Freenove/Freenove_Media_Kit_for_ESP32-S3/3D_Models/FNK0102A/3D_Shell_ESP32-S3/CB8201_Bottom.bmp

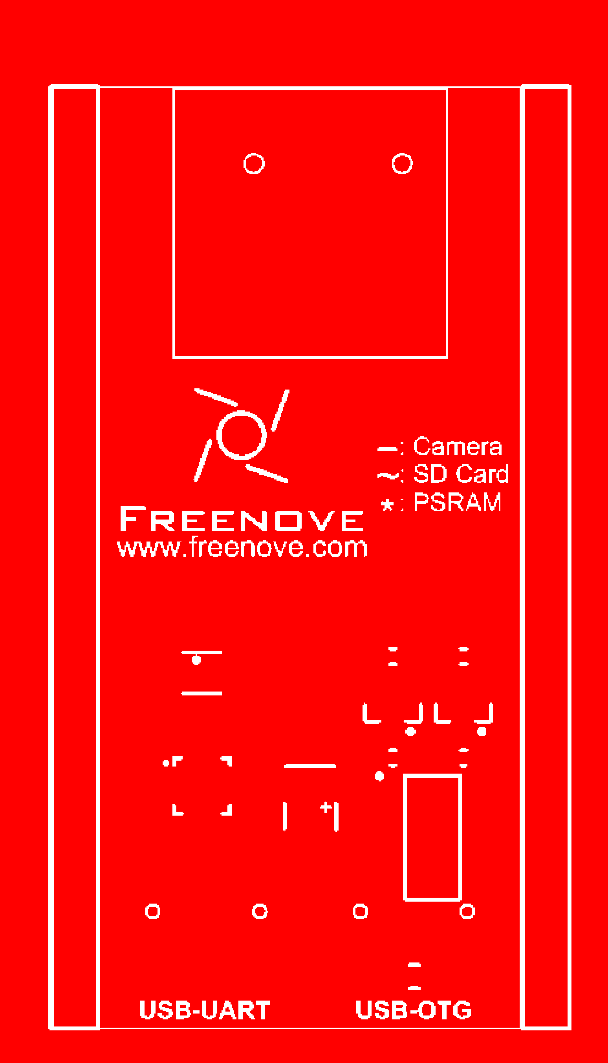
3D_Models/FNK0102A/3D_Shell_ESP32-S3/CB8201_Bottom.bmp
