Freenove/Freenove_Media_Kit_for_ESP32-S3/3D_Models/FNK0102B/3D_Shell_Media_Board/CB10202_Top.png

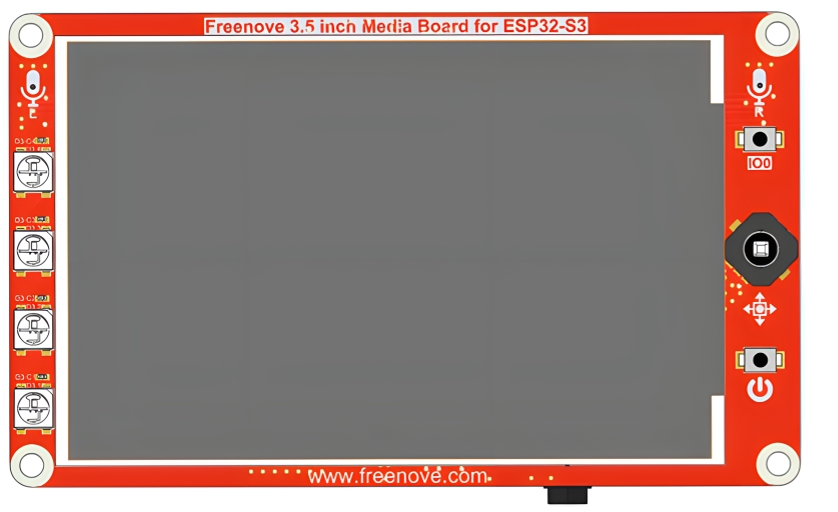
3D_Models/FNK0102B/3D_Shell_Media_Board/CB10202_Top.png
