Freenove/Freenove_Media_Kit_for_ESP32-S3/CH343/Linux/Linux.png

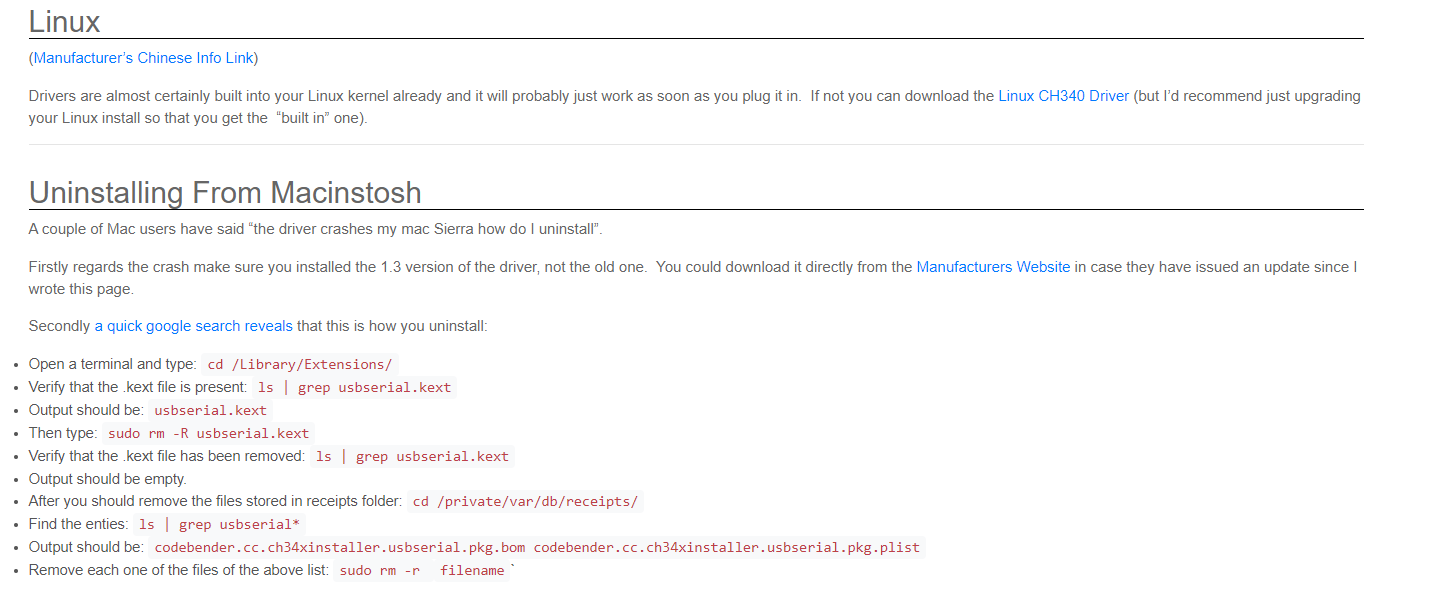
CH343/Linux/Linux.png
