Freenove/Freenove_Media_Kit_for_ESP32-S3/3D_Models/FNK0102A/3D_Shell_With_Battery/Battery_752035.SLDPRT

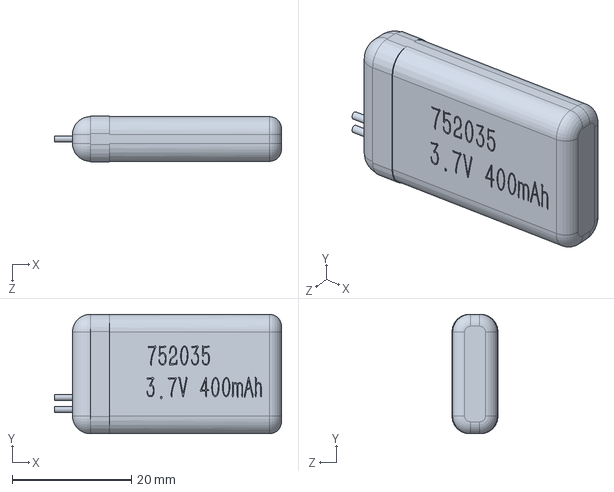
[picture p25: CAD file, 2025-04-29]
3D_Models/FNK0102A/3D_Shell_With_Battery/Battery_752035.SLDPRT
38.0 x 20.0 x 7.70 mm
