Freenove/Freenove_Media_Kit_for_ESP32-S3/3D_Models/FNK0102B/3D_Shell_Part/FNK0102B_part2_v1.0.SLDPRT

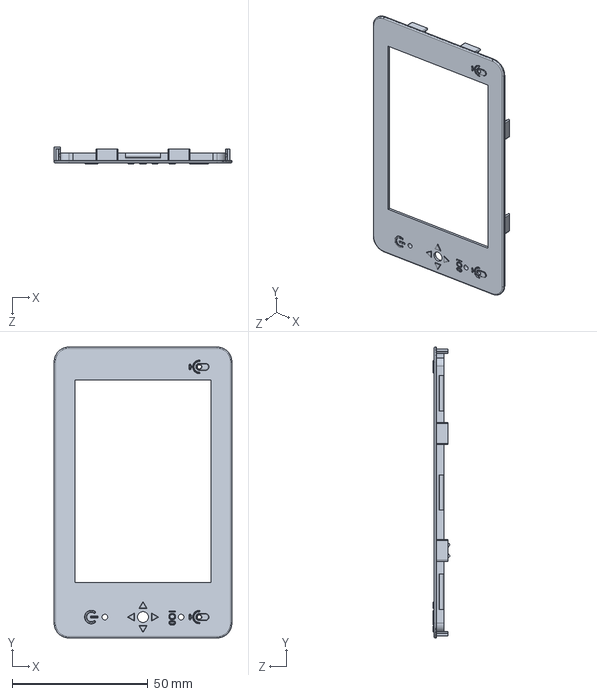
[picture p26: CAD file, 2025-12-30]
3D_Models/FNK0102B/3D_Shell_Part/FNK0102B_part2_v1.0.SLDPRT
65.4 x 107.0 x 6.12 mm
