Freenove/Freenove_Media_Kit_for_ESP32-S3/3D_Models/FNK0102A/3D_Shell_With_Battery/FNK0102_Part2_v1.2.SLDPRT

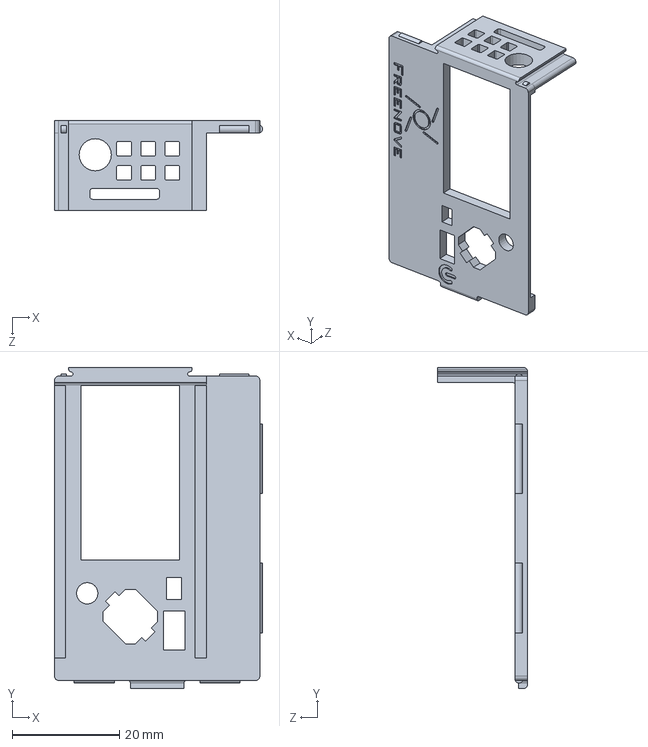
[picture p27: CAD file, 2025-04-29]
3D_Models/FNK0102A/3D_Shell_With_Battery/FNK0102_Part2_v1.2.SLDPRT
38.8 x 59.9 x 16.8 mm
