Freenove/Freenove_Media_Kit_for_ESP32-S3/Sketches/Sketch_10_1_Record_To_WAV/driver_audio_input.cpp

#include "driver_audio_input.h"

static I2SClass i2s_input;

void audio_input_init(uint8_t sck, uint8_t ws, uint8_t din) {
    i2s_input.setPins(sck, ws, -1, din);
    if (!i2s_input.begin(I2S_MODE_STD, 32000, I2S_DATA_BIT_WIDTH_32BIT, I2S_SLOT_MODE_STEREO, I2S_STD_SLOT_BOTH)) {
        Serial.println("Failed to initialize I2S bus!");
        return;
    }
    Serial.println("I2S bus initialized.");
}

void audio_input_deinit(void)
{ 
    i2s_input.end(); 
}

uint8_t* audio_input_record_wav(uint32_t duration, size_t *wav_size) {
    return i2s_input.recordWAV(duration, wav_size);
}

void audio_input_print_buffer(uint8_t* buffer, size_t size) {
    for (size_t i = 0; i < size; i++) {
        Serial.print(buffer[i]);
        Serial.print(" ");
    }
    Serial.println();
}

size_t audio_input_read_iis_data(char* buffer, size_t size) {
    return i2s_input.readBytes(buffer, size);
}

int audio_input_get_iis_data_available(void) {
    return i2s_input.available();
}
