Freenove/Freenove_Media_Kit_for_ESP32-S3/Sketches/Sketch_10_2_Record_And_Play/driver_audio_output.h

#ifndef __DRIVER_AUDIO_OUTPUT_H
#define __DRIVER_AUDIO_OUTPUT_H

#include "Arduino.h"
#include "stdint.h"

bool i2s_output_init(int bclk, int lrc, int dout);
void i2s_output_wav(uint8_t *data, size_t len);
void i2s_output_deinit(void);

int audio_output_init(int bclk, int lrc, int dout);
void audio_output_set_volume(int volume);
int audio_read_output_volume(void);
void audio_output_load_music(const char *name);
void audio_output_pause_resume(void);
void audio_output_stop(void);
bool audio_output_is_running(void);
long audio_get_total_output_playing_time(void);
long audio_output_get_file_duration(void);
bool audio_output_set_play_position(int second);
long audio_read_output_play_position(void);
void audio_output_loop(void);
void audio_info(const char *info);
void audio_eof_mp3(const char *info);






#endif
