Freenove/Freenove_Media_Kit_for_ESP32-S3/Sketches/Sketch_04_SDMMC_Test/Sketch_04_SDMMC_Test.ino

/*
* Sketch_03_SDMMC_Test.ino
* This sketch tests the SDMMC functionality using the driver_sdmmc library.
* It demonstrates initializing the SD card, listing directories, creating and removing directories,
* writing and appending to files, reading files, renaming files, and printing SD card information.
* 
* Author: [Zhentao Lin]
* Date:   [2025-04-07]
*/

#include "driver_sdmmc.h"

#define SD_MMC_CMD 38  // Please do not modify it.
#define SD_MMC_CLK 39  // Please do not modify it.
#define SD_MMC_D0 40   // Please do not modify it.

void setup() {
  // Initialize serial communication at 115200 bits per second
  Serial.begin(115200);
  // Initialize the SDMMC interface with the specified pins
  sdmmc_init(SD_MMC_CLK, SD_MMC_CMD, SD_MMC_D0);

  // List files in the root directory and print them
  std::list<File_Entry> fileList = list_dir("/", 0);
  print_file_list(fileList);

  // Create a new directory and list files again
  create_dir("/mydir");
  fileList = list_dir("/", 0);
  print_file_list(fileList);

  // Remove the directory and list files again
  remove_dir("/mydir");
  fileList = list_dir("/", 2);
  print_file_list(fileList);

  // Write text to a new file
  const char* text = "Hello ";
  write_file("/foo.txt", (const uint8_t*)text, strlen(text));

  // Append text to the existing file
  text = "World!\n";
  append_file("/foo.txt", (const uint8_t*)text, strlen(text));

  // Read the file content into a buffer and print it
  uint8_t buffer[100];
  read_file("/foo.txt", buffer, sizeof(buffer));
  Serial.write(buffer, strlen((char*)buffer));

  // Rename the file and read the new file content
  rename_file("/foo.txt", "/hello.txt");
  read_file("/hello.txt", buffer, sizeof(buffer));
  Serial.write(buffer, strlen((char*)buffer));

  // Print SD card information
  Serial.println("\r\nSD card info:");
  Serial.printf("Total space: %lluMB\r\n", SD_MMC.totalBytes() / (1024 * 1024));
  Serial.printf("Used space: %lluMB\r\n", SD_MMC.usedBytes() / (1024 * 1024));
}

void loop() {
  // Delay for 10 seconds before the next iteration
  delay(10000);
}
